flannelhead/esp8266-weather-button/include/my_config.h

/* Use the search at http://openweathermap.org/city to find this. The ID will be in the browser address bar. */
const char OWMAP_CITY_ID[] = "655195";

const int TIMEZONE_OFFSET = 2;

const char *WEEKDAYS[] = { "su", "ma", "ti", "ke", "to", "pe", "la" };
